SherpaModular/RawWaves/Software/RawWavesV2/RawWaves.h

#ifndef RawWaves_h
#define RawWaves_h

// Debug Flags
//#define DEBUG
//#define DEBUG_STARTUP // Pauses module startup until serial connection is made
//#define DEBUG_SETTINGS
//#define DEBUG_INTERFACE  was doing this before settings
//#define DEBUG_WAV
//#define DEBUG_ENGINE
//#define DEBUG_FILES
//#define DEBUG_PCM_PLAYER
//#define DEBUG_AUDIO_BUFFER

// Regularly check CPU and report via serial
//#define CHECK_CPU

// Test config modes
//#define TEST_RADIO_MODE
//#define TEST_DRUM_MODE

#endif
