SherpaModular/RawWaves/Software/RawWavesV2/Settings.h

#ifndef Settings_h
#define Settings_h

#include <SD.h>

// Classic Radio Music mode
// when true audio appears to play in the background as channels are switched.
// when false samples use the start time from CV / Pot EXCEPT in pitch mode where
// they always go back to the start.
#define LOOP_MODE_RADIO 1
// Looper Mode
// Try to keep playback position as samples are switched
#define LOOP_MODE_CONTINUE 2
// Use start point from interface
#define LOOP_MODE_START_POINT 3

class Settings {
public:
	Settings(const char* filename);
	void init();
	void read();
	void write();
	float toFloat(String settingValue);
	boolean toBoolean(String settingValue);

	uint8_t lowNote = 36;
	uint8_t noteRange = 39;

	// Which note number is normal playback speed.
	uint8_t rootNote = 60;

    boolean quantiseRootCV = true;
    boolean quantiseRootPot = true;

	uint16_t crossfadeTime = 25; // milliseconds of fade in/out on switching
	uint16_t meterHide = 2000; // how long to hide the peak meter after bank change in Milliseconds
	uint16_t startCVDivider = 2; // Changes sensitivity of Start control. 1 = most sensitive 512 = least sensitive (i.e only two points)
	boolean crossfade = false; // Crossfade clicks when changing channel / position at cost of speed. Fade speed is set by DECLICK
	boolean showMeter = true; // Does the peak meter appear?

	boolean chanPotImmediate = true; // Settings for Pot / CV response.
	boolean chanCVImmediate = true; // TRUE means it jumps directly when you move or change.

	boolean startPotImmediate = false; // FALSE means it only has an effect when RESET is pushed or triggered
	boolean startCVImmediate = false;

	boolean looping = false; // When a file finishes, start again from the beginning

	boolean sort = true; // By default we sort the directory contents.

	// Use start pot and cv to control speed instead of start point
	boolean pitchMode = false;

	// If this is true we'll read any .wav files and try to play them
	// if not we'll only play 44khz, 16bit mono files
	boolean anyAudioFiles = true;

	// Only overrides if true. Force no crossfades.
	boolean hardSwap = false;

	uint8_t loopMode = 0;

private:
	const char* _filename;
	File settingsFile;
	void radioMode();
	void drumMode();
	void applySetting(String name, String value);
};

#endif
